AbdulkadirEroglu/keybord-switchable-dock/hardware/dock/PCB_PLACEMENT.md

# Dock PCB placement groups

Parts that belong together on the dock PCB. Place each group as a cluster, then route between groups. References match `hardware/dock` (66 parts).

| # | Group | Ref | Part code | Package / footprint | Function |
|---|---|---|---|---|---|
| **1** | **Keyboard USB-C port** (board edge) | J1 | KLS L-KLS1-5416-L1-01-R | USB-C 16-pin SMD | Keyboard connector |
| | | U4 | TPD4E1U06DBVR | SOT-23-6 | ESD on D+, D−, CC1, CC2, **≤5 mm from J1** |
| | | R7, R8 | 56 kΩ | 0805 | CC pull-ups (Rp) |
| | | R9, C1 | 330 Ω, 100 nF | 0805 | Shield termination |
| **2** | **Keyboard power switch** (between `SYS_5V` and J1) | U3 | TPS2553DBVR | SOT-23-6 | 1 A current-limited switch |
| | | C6 | 1 µF | 0805 | U3 input |
| | | R5 | 26.1 kΩ | 0805 | ILIM, **short to U3 pin 5** |
| | | C7 | 1 µF | 0805 | Output, near J1 VBUS |
| | | C15, C16 | Panasonic EEE-FK1E101XP (100 µF 25 V) | 6.3 × 7.7 mm can | Keyboard VBUS bulk, **near J1 VBUS pads** |
| **3** | **Personal PC USB-C port** (board edge) | J4 | KLS L-KLS1-5416-L1-01-R | USB-C 16-pin SMD | Personal PC connector |
| | | U5 | TPD4E1U06DBVR | SOT-23-6 | ESD on D+, D−, CC1, CC2, **≤5 mm from J4** |
| | | R11, R12 | 5.1 kΩ | 0805 | CC pull-downs (Rd) |
| | | R10, C2 | 330 Ω, 100 nF | 0805 | Shield termination |
| **4** | **Work PC USB-C port** (board edge) | J5 | KLS L-KLS1-5416-L1-01-R | USB-C 16-pin SMD | Work PC connector |
| | | U6 | TPD4E1U06DBVR | SOT-23-6 | ESD on D+, D−, CC1, CC2, **≤5 mm from J5** |
| | | R15, R16 | 5.1 kΩ | 0805 | CC pull-downs (Rd) |
| | | R14, C10 | 330 Ω, 100 nF | 0805 | Shield termination |
| **5** | **Power mux** (between J4 and J5 VBUS) | U1 | TPS2116DRLR | SOT-583-8, `dock:SOT-583-8_HandSolder` (extended pads) | Personal/Work priority mux → `SYS_5V` |
| | | C9 | 1 µF | 0805 | VIN1 (Personal), **at U1 pin 3** |
| | | C8 | 1 µF | 0805 | VIN2 (Work), **at U1 pin 6** |
| | | R1, R2 | 300 kΩ, 100 kΩ | 0805 | PR1 divider (≈4.0 V switchover), **at U1 pin 4** |
| | | C3 | 1 µF | 0805 | Output |
| | | C13, C14 | Panasonic EEE-FK1E101XP (100 µF 25 V) | 6.3 × 7.7 mm can | `SYS_5V` bulk, **at U1 output** |
| **6** | **Host** (USB end → J1, **antenna end at the board edge**) | A1 | Raspberry Pi Pico 2 W | Socketed + 2 USB probes + 1×3 SWD socket | Keyboard host, router, BLE to the pad (GPIO map below) |
| | | R6 | 10 kΩ | 0805 | `KEYBOARD_VBUS_FAULT` pull-up to `HOST_3V3`, **next to A1 GP27 (pin 32) / 3V3 (pin 36)** |
| | | R3 | 10 kΩ | 0805 | `MUX_STATUS` pull-up to `HOST_3V3`, **next to A1 GP28 (pin 34) / 3V3 (pin 36)** |
| | | R24 | 10 kΩ | 0805 | `POGO_5V_FAULT` pull-up to `HOST_3V3`, **next to A1 GP18 (pin 24)** |
| | | R28 | 100 kΩ | 0805 | `KEYBOARD_VBUS_EN` pull-down to GND, **next to A1 GP26 (pin 31)** |
| | | J2 | 1×5 pin header 2.54 mm | THT | Host SWD |
| **7** | **HID-A Personal** (USB end → J4) | A2 | Raspberry Pi Pico 2 | Socketed + 4 probes | Personal PC endpoint |
| | | J3 | 1×5 pin header 2.54 mm | THT | SWD |
| | | R13 | 10 kΩ | 0805 | Role strap (GP2 → GND) |
| | | R19, R20 | 22 kΩ, 33 kΩ | 0805 | VBUS sense, **near GP4 (pin 6)** |
| | | R29, R30 | 10 kΩ | 0805 | CC sense, **near GP26/27 (pins 31/32)** |
| | | R33 | 1 kΩ | 0805 | RUN control from A1 GP2, **near A2 RUN (pin 30, right column, faces A1)** |
| | | R36 | 10 kΩ | 0805 | RUN pull-up to A2's own 3V3, **between A2 RUN (pin 30) and 3V3 (pin 36)** |
| **8** | **HID-B Work** (USB end → J5) | A3 | Raspberry Pi Pico 2 | Socketed + 4 probes | Work PC endpoint |
| | | J6 | 1×5 pin header 2.54 mm | THT | SWD |
| | | R17 | 10 kΩ | 0805 | Role strap (GP2 → 3V3) |
| | | R21, R22 | 22 kΩ, 33 kΩ | 0805 | VBUS sense, near GP4 (pin 6) |
| | | R31, R32 | 10 kΩ | 0805 | CC sense, near GP26/27 (pins 31/32) |
| | | R34 | 1 kΩ | 0805 | RUN control from A1 GP19, **near J6 pin 4 or A3 RUN (pin 30)** |
| | | R37 | 10 kΩ | 0805 | RUN pull-up to A3's own 3V3, **between A3 RUN (pin 30) and 3V3 (pin 36)** |
| **9** | **Pogo interface** (pad-docking edge) | J7 | 6-pin pogo connector | `dock:Pogo-6` | GND, +5V, DET, RX, TX, GND |
| | | U9 | TPD4E1U06DBVR | SOT-23-6 | ESD, **right at J7** |
| | | R25, R26, R27 | 1 kΩ | 0805 | Series resistors on TX/RX/DET, between U9 and the host (GP16/GP17/GP22) |
| | | R18 | 10 kΩ | 0805 | `POGO_DET` pull-up to `HOST_3V3` |
| | | U8 | TPS2552DBVR | SOT-23-6 | Pogo +5V switch, on when docked |
| | | C11, C12 | 1 µF | 0805 | U8 in/out |
| | | R23 | 26.1 kΩ | 0805 | U8 ILIM |

## Pull-ups and pull-downs: where they go

A pull resistor connects the same two nets wherever it sits, so place it where its supply is: next to the 3V3 pin it pulls up to (or near GND). The signal line itself runs to the far chip.

| Ref | Pulls | To | Place near |
|---|---|---|---|
| R3, R6, R24 | `MUX_STATUS`, `KEYBOARD_VBUS_FAULT`, `POGO_5V_FAULT` | `HOST_3V3` (A1 pin 36) | A1 right column |
| R28 | `KEYBOARD_VBUS_EN` | GND | A1 GP26 |
| R36 / R37 | HID-A / HID-B RUN | that Pico's own 3V3 | each Pico's right column (RUN pin 30, 3V3 pin 36) |
| R13 / R17 | HID-A / HID-B role strap (GP2) | GND / that Pico's 3V3 | each Pico's GP2 (pin 4) |
| R18 | `POGO_DET` | `HOST_3V3` (A1 pin 36) | pogo group or A1 right column |

## Pico GPIO map (physical pins)

Pin 1 is top-left with the USB end up; left column is pins 1–20 top to bottom, right column pins 40–21 top to bottom.

| Module | Signal | GPIO | Pin | Side |
|---|---|---|---|---|
| A1 host | UART0 TX → HID-A (`HID_PERSONAL_TX`) | GP12 | 16 | left, lower |
| A1 host | UART0 RX ← HID-A (`HID_PERSONAL_RX`) | GP13 | 17 | left, lower |
| A1 host | UART1 TX → HID-B (`HID_WORK_TX`) | GP20 | 26 | right, lower |
| A1 host | UART1 RX ← HID-B (`HID_WORK_RX`) | GP21 | 27 | right, lower |
| A1 host | PIO TX → pogo (`POGO_TX`) | GP16 | 21 | right, bottom |
| A1 host | PIO RX ← pogo (`POGO_RX`) | GP17 | 22 | right, bottom |
| A1 host | `KEYBOARD_VBUS_EN` / `_FAULT` | GP26 / GP27 | 31 / 32 | right, upper |
| A1 host | `MUX_STATUS` | GP28 | 34 | right, upper |
| A1 host | `POGO_5V_FAULT` | GP18 | 24 | right, lower |
| A1 host | `HID_PERSONAL_RUN_CTRL` | GP2 | 4 | left, top |
| A1 host | `HID_WORK_RUN_CTRL` | GP19 | 25 | right, lower |
| A1 host | `POGO_DET` input | GP22 | 29 | right, middle |
| A1 host | SWD (SWCLK / GND / SWDIO) | debug holes | — | middle, 19.8 mm from the antenna end, via 1×3 socket |
| A2 HID-A | UART0 TX / RX | GP16 / GP17 | 21 / 22 | right, bottom (faces A1) |
| A3 HID-B | UART0 TX / RX | GP12 / GP13 | 16 / 17 | left, lower (faces A1) |
| A1, A2, A3 | VSYS (`SYS_5V`) | — | 39 | right, top |

## Parts not on the schematic (mechanical)

| Item | Qty | Part code | Notes |
|---|---|---|---|
| Female socket, 1×20, 2.54 mm, 8.5 mm tall | 6 | generic | 2 per Pico, on the dock |
| Female socket, 1×3, 2.54 mm | 1 | generic (cut from a longer strip) | Host SWD, on the dock |
| Male pin header, 1×20 / 1×3, 2.54 mm | 6 + 1 | generic | Soldered to the Picos (1×3 on the host's debug holes, pointing down) |
| Spring probe | 10 required, +5 optional | P50-B1 | A1 (Pico 2 W): TP2, TP3 (+TP1). A2/A3 (Pico 2): TP2, TP3, D1, D3 (+TP1, D2 GND) |

## Placement rules

- ESD parts (U4, U5, U6, U9) sit right at their connectors. Protection only works when the surge hits the ESD part first.
- Keep the D+/D− pairs short and direct: connector → ESD → the Pico's TP2/TP3 probe holes, with the Pico's USB end pointing at its connector. Route them as differential pairs (USB net class).
- Nothing under the modules except the probes. Probe tails stick out about 2.7 mm below the board at each HID Pico's two ends and at the host's USB end, so keep bottom-side parts away from those spots.
- Host (Pico 2 W) antenna end: at a board edge, with no copper under it and nothing in front of it. The footprint's 14 × 9 mm keep-out zone enforces the copper part. Use a non-metal enclosure.
- SWD headers J2, J3, J6: along one edge you can reach with the lid off.
- Power nets (`SYS_5V`, `PERSONAL_VBUS`, `WORK_VBUS`, `KEYBOARD_VBUS`, `POGO_5V`, GND) use the Power net class (0.6 mm); keep the U1 → C13/C14 → loads path short and wide.
- Board outline: 100 × 100 mm (60.5, 25.5) – (160.5, 125.5). The host sits at the bottom edge with its antenna end on the edge; the pogo group goes to a bottom corner, clear of the antenna.

## Routing techniques

- **Route under the modules.** A socketed Pico sits ≈11 mm above the board; the 17.8 mm between its socket rows is free board apart from the probe holes at its two ends. One 0.2 mm track fits between adjacent socket pins (2.54 mm pitch).
- **`SYS_5V` trunk.** Run one wide horizontal track below the connector area and drop short branches to each Pico's pin 39 (top-right corner); one branch continues down the side to U8 and J7.
- **USB-C pad trick.** With the connectors rotated 180°, the D+/D− pads read D+ (B6), D− (A7), D+ (A6), D− (B7) from left to right. Take the pair to the Pico from B6/A7 (D+ left, D− right, the Pico's order). Join A6 → B6 and B7 → A7 with one short jumper through two vias under the connector.
- **ESD flow-through.** D+ over U4/U5/U6 pin 1 (left), D− over pin 6 (right); CC lines on pins 3/4. Any TPD4E1U06 channel can carry any signal if a different order routes better (change it in the schematic, then F8).
- **GND** goes to the B.Cu plane; SMD GND pads get a via next to the pad.
